jwidess/ESP-Arduino-TFT-Weather/TFT-Driver-Mk1/src/bitmaps.h

#ifndef BITMAPS_H
#define BITMAPS_H

// Small bitmaps

static const unsigned char PROGMEM image_Chance_of_Rain_Symbol_bits[] = {0x00, 0x00, 0x00, 0x00, 0x00, 0x00, 0x00, 0x00, 0x00, 0x03, 0x00, 0x00, 0x00, 0x03, 0x00, 0x00, 0x00, 0x3f, 0xf0, 0x00, 0x00, 0x3f, 0xf0, 0x00, 0x03, 0xff, 0xff, 0x00, 0x03, 0xff, 0xff, 0x00, 0x0f, 0xff, 0xff, 0xc0, 0x0f, 0xff, 0xff, 0xc0, 0x3f, 0xff, 0xff, 0xf0, 0x3f, 0xff, 0xff, 0xf0, 0xff, 0xff, 0xff, 0xfc, 0xff, 0xff, 0xff, 0xfc, 0x00, 0x03, 0x00, 0x00, 0x00, 0x03, 0x00, 0x00, 0x00, 0x03, 0x00, 0x00, 0x00, 0x03, 0x00, 0x00, 0x00, 0x03, 0x00, 0x00, 0x00, 0x03, 0x00, 0x00, 0x00, 0x03, 0x00, 0x00, 0x00, 0x03, 0x00, 0x00, 0x00, 0x03, 0x00, 0x00, 0x00, 0x03, 0x00, 0x00, 0x00, 0x03, 0x00, 0x00, 0x00, 0x03, 0x00, 0x00, 0x00, 0x33, 0x00, 0x00, 0x00, 0x33, 0x00, 0x00, 0x00, 0x0c, 0x00, 0x00, 0x00, 0x0c, 0x00, 0x00, 0x00, 0x00, 0x00, 0x00, 0x00, 0x00, 0x00, 0x00};

static const unsigned char PROGMEM image_Humidity_Symbol_bits[] = {0x00, 0x80, 0x00, 0x00, 0x80, 0x00, 0x00, 0x80, 0x00, 0x03, 0x80, 0x00, 0x03, 0x60, 0x00, 0x03, 0x60, 0x00, 0x04, 0x60, 0x00, 0x04, 0x60, 0x00, 0x04, 0x10, 0x00, 0x18, 0x0c, 0x00, 0x18, 0x0c, 0x00, 0x18, 0x0c, 0x00, 0x20, 0x12, 0x00, 0x20, 0x12, 0x00, 0x20, 0x0e, 0x00, 0xc0, 0x0d, 0x80, 0xc0, 0x0d, 0x80, 0xc0, 0x01, 0x80, 0x20, 0x02, 0x00, 0x20, 0x02, 0x00, 0x20, 0x02, 0x00, 0x1c, 0x0c, 0x00, 0x1c, 0x0c, 0x00, 0x03, 0xf0, 0x00};

// ====================================================================================================================================
// Large bitmaps

// Weather Sunny (90, 96) e.g. tft.drawBitmap(x, y, image_weather_sunny_bits, 90, 96, 0xFFFF);
static const unsigned char PROGMEM image_weather_sunny_bits[] = {0x00, 0x00, 0x00, 0x00, 0x00, 0x3f, 0x00, 0x00, 0x00, 0x00, 0x00, 0x00, 0x00, 0x00, 0x00, 0x00, 0x00, 0x3f, 0x00, 0x00, 0x00, 0x00, 0x00, 0x00, 0x00, 0x00, 0x00, 0x00, 0x00, 0x3f, 0x00, 0x00, 0x00, 0x00, 0x00, 0x00, 0x00, 0x00, 0x00, 0x00, 0x00, 0x3f, 0x00, 0x00, 0x00, 0x00, 0x00, 0x00, 0x00, 0x00, 0x00, 0x00, 0x00, 0x3f, 0x00, 0x00, 0x00, 0x00, 0x00, 0x00, 0x00, 0x00, 0x00, 0x00, 0x00, 0x3f, 0x00, 0x00, 0x00, 0x00, 0x00, 0x00, 0x00, 0x0f, 0xc0, 0x00, 0x00, 0x3f, 0x00, 0x00, 0x00, 0xfc, 0x00, 0x00, 0x00, 0x0f, 0xc0, 0x00, 0x00, 0x3f, 0x00, 0x00, 0x00, 0xfc, 0x00, 0x00, 0x00, 0x0f, 0xc0, 0x00, 0x00, 0x3f, 0x00, 0x00, 0x00, 0xfc, 0x00, 0x00, 0x00, 0x0f, 0xc0, 0x00, 0x00, 0x3f, 0x00, 0x00, 0x00, 0xfc, 0x00, 0x00, 0x00, 0x0f, 0xc0, 0x00, 0x00, 0x3f, 0x00, 0x00, 0x00, 0xfc, 0x00, 0x00, 0x00, 0x0f, 0xc0, 0x00, 0x00, 0x3f, 0x00, 0x00, 0x00, 0xfc, 0x00, 0x00, 0x00, 0x00, 0x3f, 0x00, 0x00, 0x00, 0x00, 0x00, 0x3f, 0x00, 0x00, 0x00, 0x00, 0x00, 0x3f, 0x00, 0x00, 0x00, 0x00, 0x00, 0x3f, 0x00, 0x00, 0x00, 0x00, 0x00, 0x3f, 0x00, 0x00, 0x00, 0x00, 0x00, 0x3f, 0x00, 0x00, 0x00, 0x00, 0x00, 0x3f, 0x00, 0x00, 0x00, 0x00, 0x00, 0x3f, 0x00, 0x00, 0x00, 0x00, 0x00, 0x3f, 0x00, 0x00, 0x00, 0x00, 0x00, 0x3f, 0x00, 0x00, 0x00, 0x00, 0x00, 0x3f, 0x00, 0x00, 0x00, 0x00, 0x00, 0x3f, 0x00, 0x00, 0x00, 0x00, 0x00, 0x00, 0x00, 0x0f, 0xff, 0xfc, 0x00, 0x00, 0x00, 0x00, 0x00, 0x00, 0x00, 0x00, 0x00, 0x0f, 0xff, 0xfc, 0x00, 0x00, 0x00, 0x00, 0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

// Weather Cloudy Sunny (85, 80) e.g. tft.drawBitmap(x, y, image_weather_cloudy_sunny_bits, 85, 80, 0xFFFF);
static const unsigned char PROGMEM image_weather_cloudy_sunny_bits[] = {0x00,0x00,0x00,0x00,0x00,0x00,0x3e,0x00,0x00,0x00,0x00,0x00,0x00,0x00,0x00,0x00,0x00,0x3e,0x00,0x00,0x00,0x00,0x00,0x00,0x00,0x00,0x00,0x00,0x3e,0x00,0x00,0x00,0x00,0x00,0x00,0x00,0x00,0x00,0x00,0x3e,0x00,0x00,0x00,0x00,0x00,0x00,0x00,0x00,0x00,0x00,0x3e,0x00,0x00,0x00,0x00,0x00,0x00,0x00,0x03,0xe0,0x00,0x00,0x00,0x03,0xe0,0x00,0x00,0x00,0x00,0x03,0xe0,0x00,0x00,0x00,0x03,0xe0,0x00,0x00,0x00,0x00,0x03,0xe0,0x00,0x00,0x00,0x03,0xe0,0x00,0x00,0x00,0x00,0x03,0xe0,0x00,0x00,0x00,0x03,0xe0,0x00,0x00,0x00,0x00,0x03,0xe0,0x00,0x00,0x00,0x03,0xe0,0x00,0x00,0x00,0x00,0x00,0x00,0x07,0xff,0xf0,0x00,0x00,0x00,0x00,0x00,0x00,0x00,0x00,0x07,0xff,0xf0,0x00,0x00,0x00,0x00,0x00,0x00,0x00,0x00,0x07,0xff,0xf0,0x00,0x00,0x00,0x00,0x00,0x00,0x00,0x00,0x07,0xff,0xf0,0x00,0x00,0x00,0x00,0x00,0x00,0x00,0x00,0x07,0xff,0xf0,0x00,0x00,0x00,0x00,0x00,0x00,0x00,0x1f,0xf8,0x00,0x0f,0xfc,0x00,0x00,0x00,0x00,0x00,0x00,0x1f,0xf8,0x00,0x0f,0xfc,0x00,0x00,0x00,0x00,0x00,0x00,0x1f,0xf8,0x00,0x0f,0xfc,0x00,0x00,0x00,0x00,0x00,0x00,0x1f,0xf8,0x00,0x0f,0xfc,0x00,0x00,0x00,0x00,0x00,0x00,0x1f,0xf8,0x00,0x0f,0xfc,0x00,0x00,0x00,0x00,0x0f,0x80,0x1f,0x00,0x00,0x00,0x7c,0x00,0xf8,0x00,0x00,0x0f,0x80,0x1f,0x00,0x00,0x00,0x7c,0x00,0xf8,0x00,0x00,0x0f,0x80,0x1f,0x00,0x00,0x00,0x7c,0x00,0xf8,0x00,0x00,0x0f,0x80,0x1f,0x00,0x00,0x00,0x7c,0x00,0xf8,0x00,0x00,0x0f,0x80,0x1f,0x00,0x00,0x00,0x7c,0x00,0xf8,0x00,0x00,0x00,0x03,0xe0,0x00,0x00,0x00,0x03,0xe0,0x0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

//Weather Exceptional () e.g. tft.drawBitmap(10, 6, image_weather_exceptional_bits, 90, 90, 0xFFFF);
static const unsigned char PROGMEM image_weather_exceptional_bits[] = {0x00,0x00,0x00,0x00,0x00,0x00,0x00,0x00,0x00,0x00,0x00,0x00,0x7f,0xff,0x80,0x00,0x00,0x00,0x00,0x00,0x00,0x7f,0xff,0x80,0x7f,0xff,0x80,0x00,0x00,0x00,0x00,0x00,0x00,0x7f,0xff,0x80,0x7f,0xff,0x80,0x00,0x00,0x00,0x00,0x00,0x00,0x7f,0xff,0x80,0x7f,0xff,0x80,0x00,0x00,0x00,0x00,0x00,0x00,0x7f,0xff,0x80,0x7f,0xff,0x80,0x00,0x00,0x00,0x00,0x00,0x00,0x7f,0xff,0x80,0x7f,0xff,0x80,0x00,0x00,0x00,0x00,0x00,0x00,0x7f,0xff,0x80,0x7f,0xff,0x80,0x00,0x00,0x00,0x00,0x00,0x00,0x7f,0xff,0x80,0x7f,0xff,0x80,0x00,0x00,0x00,0x00,0x00,0x00,0x7f,0xff,0x80,0x7f,0xff,0xff,0x80,0x00,0x00,0x00,0x00,0x7f,0xff,0xff,0x80,0x7f,0xff,0xff,0x80,0x00,0x00,0x00,0x00,0x7f,0xff,0xff,0x80,0x7f,0xff,0xff,0x80,0x00,0x00,0x00,0x00,0x7f,0xff,0xff,0x80,0x7f,0xff,0xff,0x80,0x00,0x00,0x00,0x00,0x7f,0xff,0xff,0x80,0x7f,0xff,0xff,0x80,0x00,0x00,0x00,0x00,0x7f,0xff,0xff,0x80,0x7f,0xff,0xff,0x80,0x00,0x00,0x00,0x00,0x7f,0xff,0xff,0x80,0x7f,0xff,0xff,0x80,0x00,0x00,0x00,0x00,0x7f,0xff,0xff,0x80,0x7f,0xff,0xff,0x80,0x00,0x00,0x00,0x00,0x7f,0xff,0xff,0x80,0x00,0x7f,0xff,0xff,0x80,0x00,0x00,0x7f,0xff,0xff,0x80,0x00,0x00,0x7f,0xff,0xff,0x80,0x00,0x00,0x7f,0xff,0xff,0x80,0x00,0x00,0x7f,0xff,0xff,0x80,0x00,0x00,0x7f,0xff,0xff,0x80,0x00,0x00,0x7f,0xff,0xff,0x80,0x00,0x00,0x7f,0xff,0xff,0x80,0x00,0x00,0x7f,0xff,0xff,0x80,0x00,0x00,0x7f,0xff,0xff,0x80,0x00,0x00,0x7f,0xff,0xff,0x80,0x00,0x00,0x7f,0xff,0xff,0x80,0x00,0x00,0x7f,0xff,0xff,0x80,0x00,0x00,0x7f,0xff,0xff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

#endif // BITMAPS_H
